MathieuMaisonnette/Digital-effect-Guitar-Pedal/pics/6.png

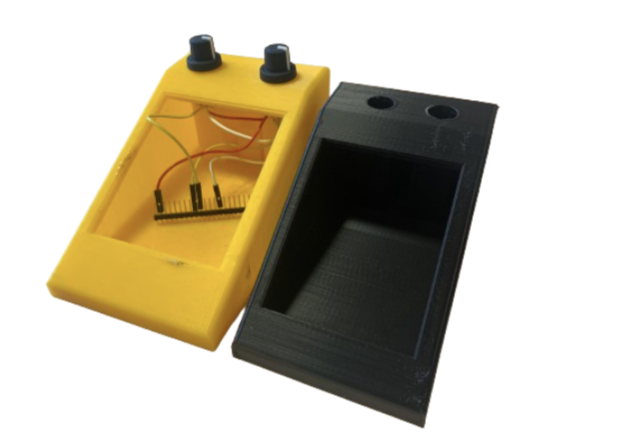
pics/6.png
